supermomo31/PCE_colorlight_carrier/PCE_Colorlight_Carrier/av.kicad_sch

## KiCad design PCE_Colorlight_Carrier/av.kicad_sch (2026-05-21, an earlier design)

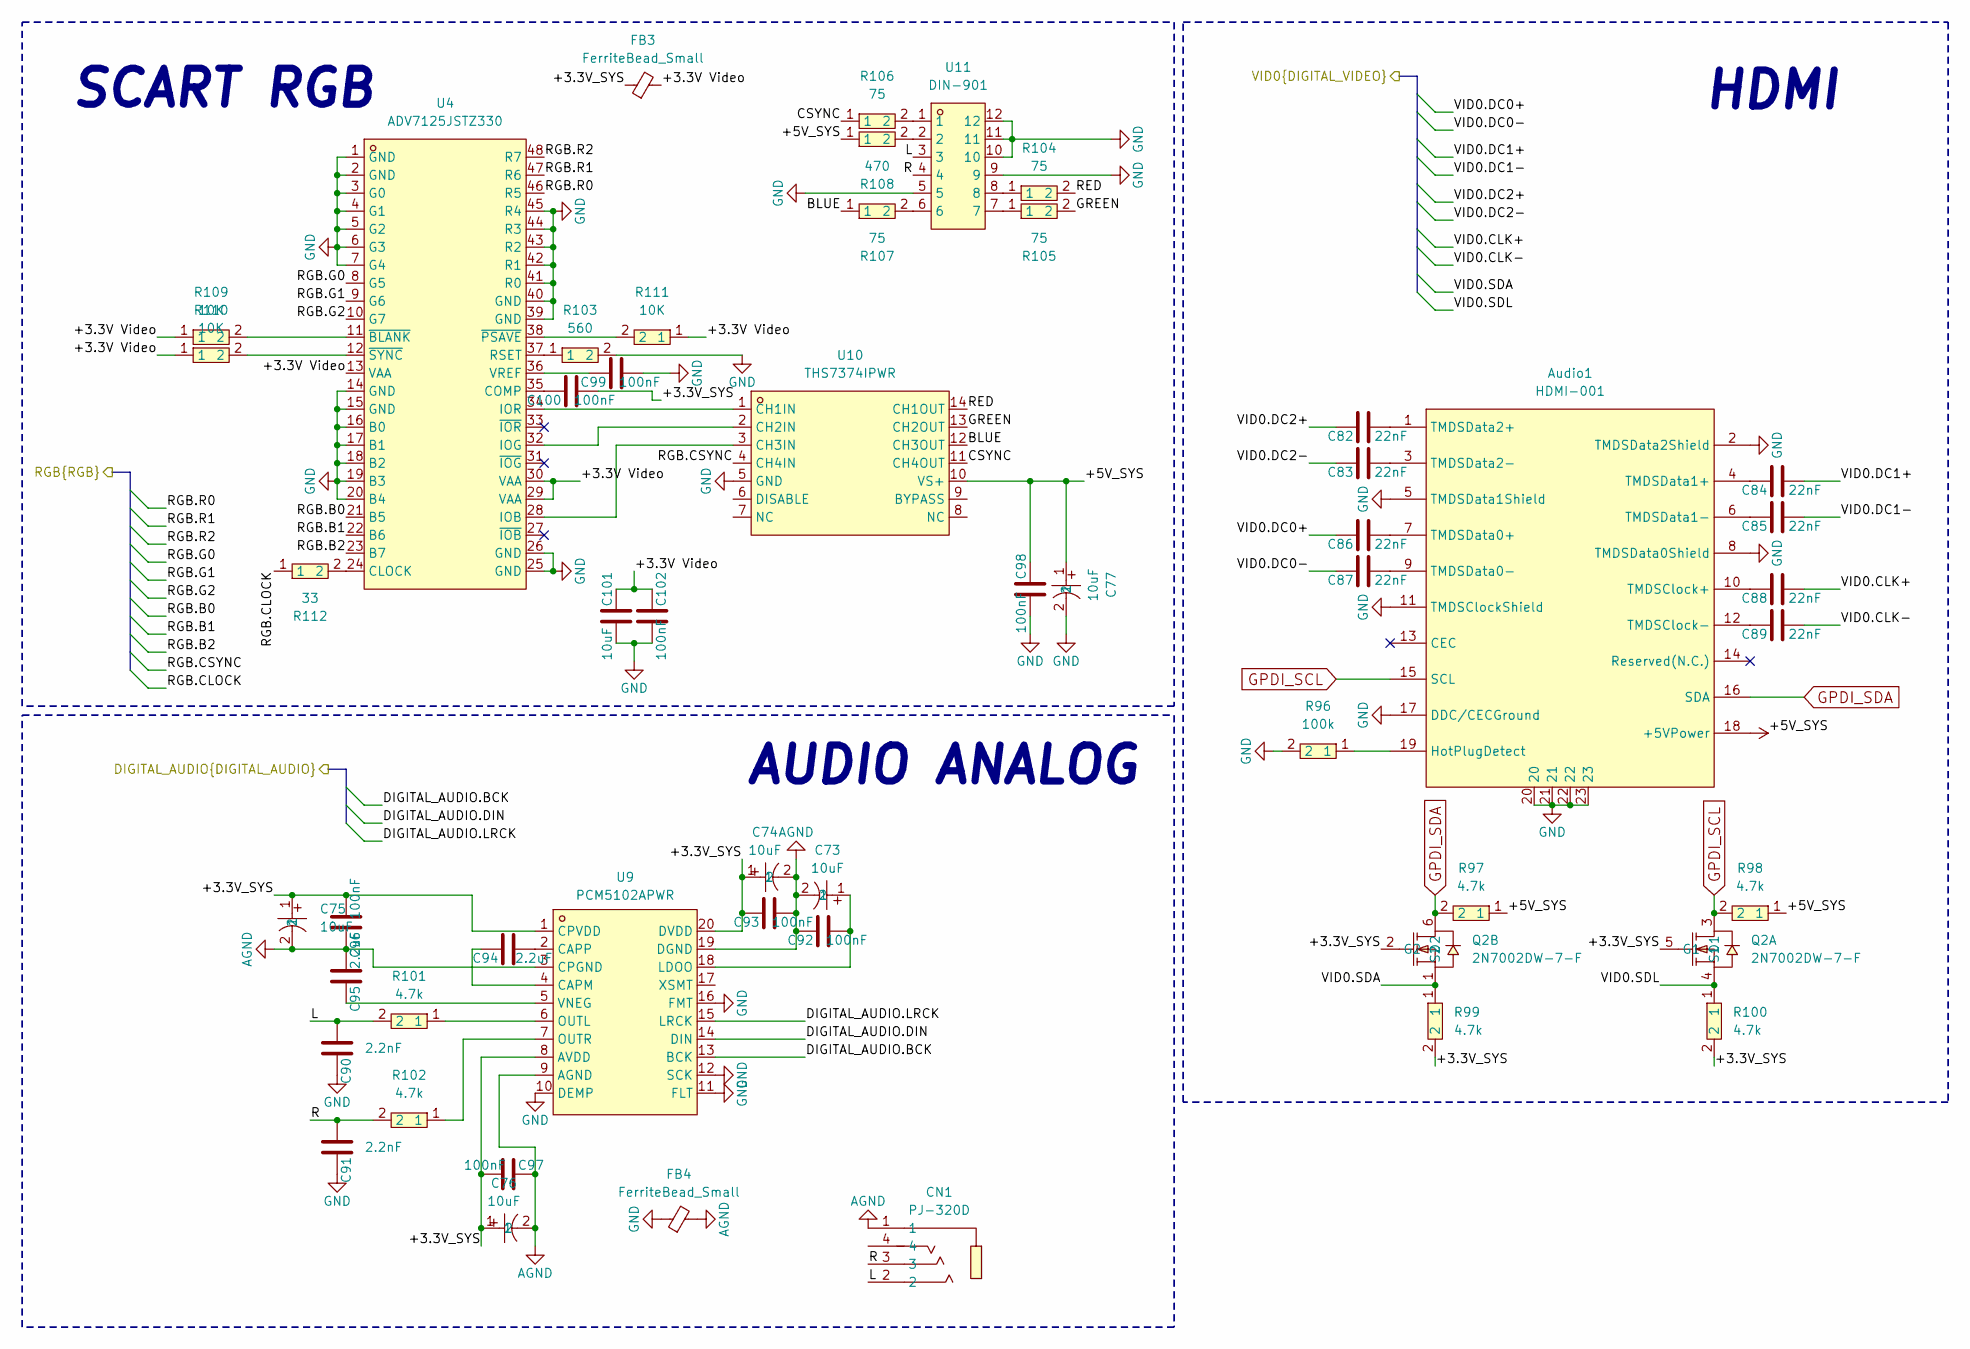
[picture p3: schematic av.kicad_sch]

Parts:
Audio1: HDMI-001; HDMI; MPN HDMI-001 19PCBTP; LCSC Part C138388
C73, C74, C75, C76, C77: 10uF; CAP-SMD_BD5.0-L5.3-W5.3-FD; MPN RVT1A101M0505; LCSC Part C3347
C82, C83, C84, C85, C86, C87, C88, C89: 22nF; C_0603_1608Metric
C90, C91: 2.2nF; C_0603_1608Metric
C92, C93, C96, C97, C98, C99, C100, C102: 100nF; C_0603_1608Metric
C94, C95: 2.2uF; C_0603_1608Metric
C101: 10uF; C_0603_1608Metric
CN1: PJ-320D; AUDIO-SMD_PJ-320D-1; MPN PJ-320D; LCSC Part C431535
FB3, FB4: FerriteBead_Small
Q2: 2N7002DW-7-F; SOT-363_L2.0-W1.3-P0.65-LS2.1-TL; MPN 2N7002DW-7-F; LCSC Part C83571
R96: 100k; R0603; MPN 0603WAF5101T5E; LCSC Part C23186
R97, R98, R99, R100, R101, R102: 4.7k; R0603; MPN 0603WAF5101T5E; LCSC Part C23186
R103: 560; R0603; MPN 0603WAF5101T5E; LCSC Part C23186
R104, R105, R106, R107: 75; R0603; MPN 0603WAF5101T5E; LCSC Part C23186
R108: 470; R0603; MPN 0603WAF5101T5E; LCSC Part C23186
R109, R110, R111: 10K; R0603; MPN 0603WAF5101T5E; LCSC Part C23186
R112: 33; R0603; MPN 0603WAF5101T5E; LCSC Part C23186
U4: ADV7125JSTZ330; LQFP-48_L7.0-W7.0-P0.50-LS9.0-BL; MPN ADV7125JSTZ330; LCSC Part C662165
U9: PCM5102APWR; MPN PCM5102APWR; LCSC Part C107671
U10: THS7374IPWR; MPN THS7374IPWR; LCSC Part C2652746
U11: DIN-901; mini din 9; MPN DIN-901; LCSC Part C23689425

Connections:
+3.3V Video: C101.1, C102.1, FB3.2, R109.1, R110.1, R111.1, U4.13 (VAA), U4.29 (VAA), U4.30 (VAA)
+3.3V_SYS: C74.1, C75.1, C76.1, C93.1, C96.2, C97.2, C100.2, FB3.1, Q2.2 (G2), Q2.5 (G1), R99.2, R100.2, U9.1 (CPVDD), U9.8 (AVDD), U9.20 (DVDD)
+5V: Audio1.18 (+5VPower)
+5V_SYS: C77.1, C98.1, R97.1, R98.1, R108.1, U10.10 (VS+)
AGND: C73.2, C74.2, C75.2, C76.2, C92.1, C93.2, C95.2, C96.1, C97.1, CN1.1, FB4.2, U9.3 (CPGND), U9.9 (AGND), U9.19 (DGND)
BLUE: R107.1, U10.12 (CH3OUT)
CSYNC: R106.1, U10.11 (CH4OUT)
DIGITAL_AUDIO.BCK: U9.13 (BCK)
DIGITAL_AUDIO.DIN: U9.14 (DIN)
DIGITAL_AUDIO.LRCK: U9.15 (LRCK)
GND: Audio1.2 (TMDSData2Shield), Audio1.5 (TMDSData1Shield), Audio1.8 (TMDSData0Shield), Audio1.11 (TMDSClockShield), Audio1.17 (DDC/CECGround), Audio1.20, Audio1.21, Audio1.22, Audio1.23, C77.2, C90.1, C91.1, C98.2, C99.2, C101.2, C102.2, FB4.1, R96.2, R103.2, U4.1 (GND), U4.2 (GND), U4.3 (G0), U4.4 (G1), U4.5 (G2), U4.6 (G3), U4.7 (G4), U4.14 (GND), U4.15 (GND), U4.16 (B0), U4.17 (B1), U4.18 (B2), U4.19 (B3), U4.20 (B4), U4.25 (GND), U4.26 (GND), U4.39 (GND), U4.40 (GND), U4.41 (R0), U4.42 (R1), U4.43 (R2), U4.44 (R3), U4.45 (R4), U9.10 (DEMP), U9.11 (FLT), U9.12 (SCK), U9.16 (FMT), U10.5 (GND), U11.5, U11.9, U11.10, U11.11, U11.12
GPDI_SCL: Audio1.15 (SCL), Q2.3 (D1), R98.2
GPDI_SDA: Audio1.16 (SDA), Q2.6 (D2), R97.2
GREEN: R105.2, U10.13 (CH2OUT)
L: C90.2, CN1.2, R101.2, U11.3
unnamed: Audio1.1 (TMDSData2+), C82.2
unnamed: Audio1.3 (TMDSData2-), C83.2
unnamed: Audio1.4 (TMDSData1+), C84.1
unnamed: Audio1.6 (TMDSData1-), C85.1
unnamed: Audio1.7 (TMDSData0+), C86.2
unnamed: Audio1.9 (TMDSData0-), C87.2
unnamed: Audio1.10 (TMDSClock+), C88.1
unnamed: Audio1.12 (TMDSClock-), C89.1
unnamed: Audio1.19 (HotPlugDetect), R96.1
unnamed: C73.1, C92.2, U9.18 (LDOO)
unnamed: C94.1, U9.4 (CAPM)
unnamed: C94.2, U9.2 (CAPP)
unnamed: C95.1, U9.5 (VNEG)
unnamed: C99.1, U4.36 (VREF)
unnamed: C100.1, U4.35 (COMP)
unnamed: R101.1, U9.6 (OUTL)
unnamed: R102.1, U9.7 (OUTR)
unnamed: R103.1, U4.37 (RSET)
unnamed: R104.1, U11.8
unnamed: R105.1, U11.7
unnamed: R106.2, U11.1
unnamed: R107.2, U11.6
unnamed: R108.2, U11.2
unnamed: R109.2, U4.11 (~BLANK)
unnamed: R110.2, U4.12 (~SYNC)
unnamed: R111.2, U4.38 (~PSAVE)
unnamed: R112.2, U4.24 (CLOCK)
unnamed: U4.34 (IOR), U10.1 (CH1IN)
unnamed: U4.32 (IOG), U10.2 (CH2IN)
unnamed: U4.28 (IOB), U10.3 (CH3IN)
R: C91.2, CN1.3, R102.2, U11.4
RED: R104.2, U10.14 (CH1OUT)
RGB.B0: U4.21 (B5)
RGB.B1: U4.22 (B6)
RGB.B2: U4.23 (B7)
RGB.CLOCK: R112.1
RGB.CSYNC: U10.4 (CH4IN)
RGB.G0: U4.8 (G5)
RGB.G1: U4.9 (G6)
RGB.G2: U4.10 (G7)
RGB.R0: U4.46 (R5)
RGB.R1: U4.47 (R6)
RGB.R2: U4.48 (R7)
VID0.CLK+: C88.2
VID0.CLK-: C89.2
VID0.DC0+: C86.1
VID0.DC0-: C87.1
VID0.DC1+: C84.2
VID0.DC1-: C85.2
VID0.DC2+: C82.1
VID0.DC2-: C83.1
VID0.SDA: Q2.1 (S2), R99.1
VID0.SDL: Q2.4 (S1), R100.1

Notes on the sheet:
AUDIO ANALOG
SCART RGB
HDMI
