supermomo31/PCE_colorlight_carrier/PCE_Colorlight_Carrier/core.kicad_sch

## KiCad design PCE_Colorlight_Carrier/core.kicad_sch (2026-05-21, an earlier design)

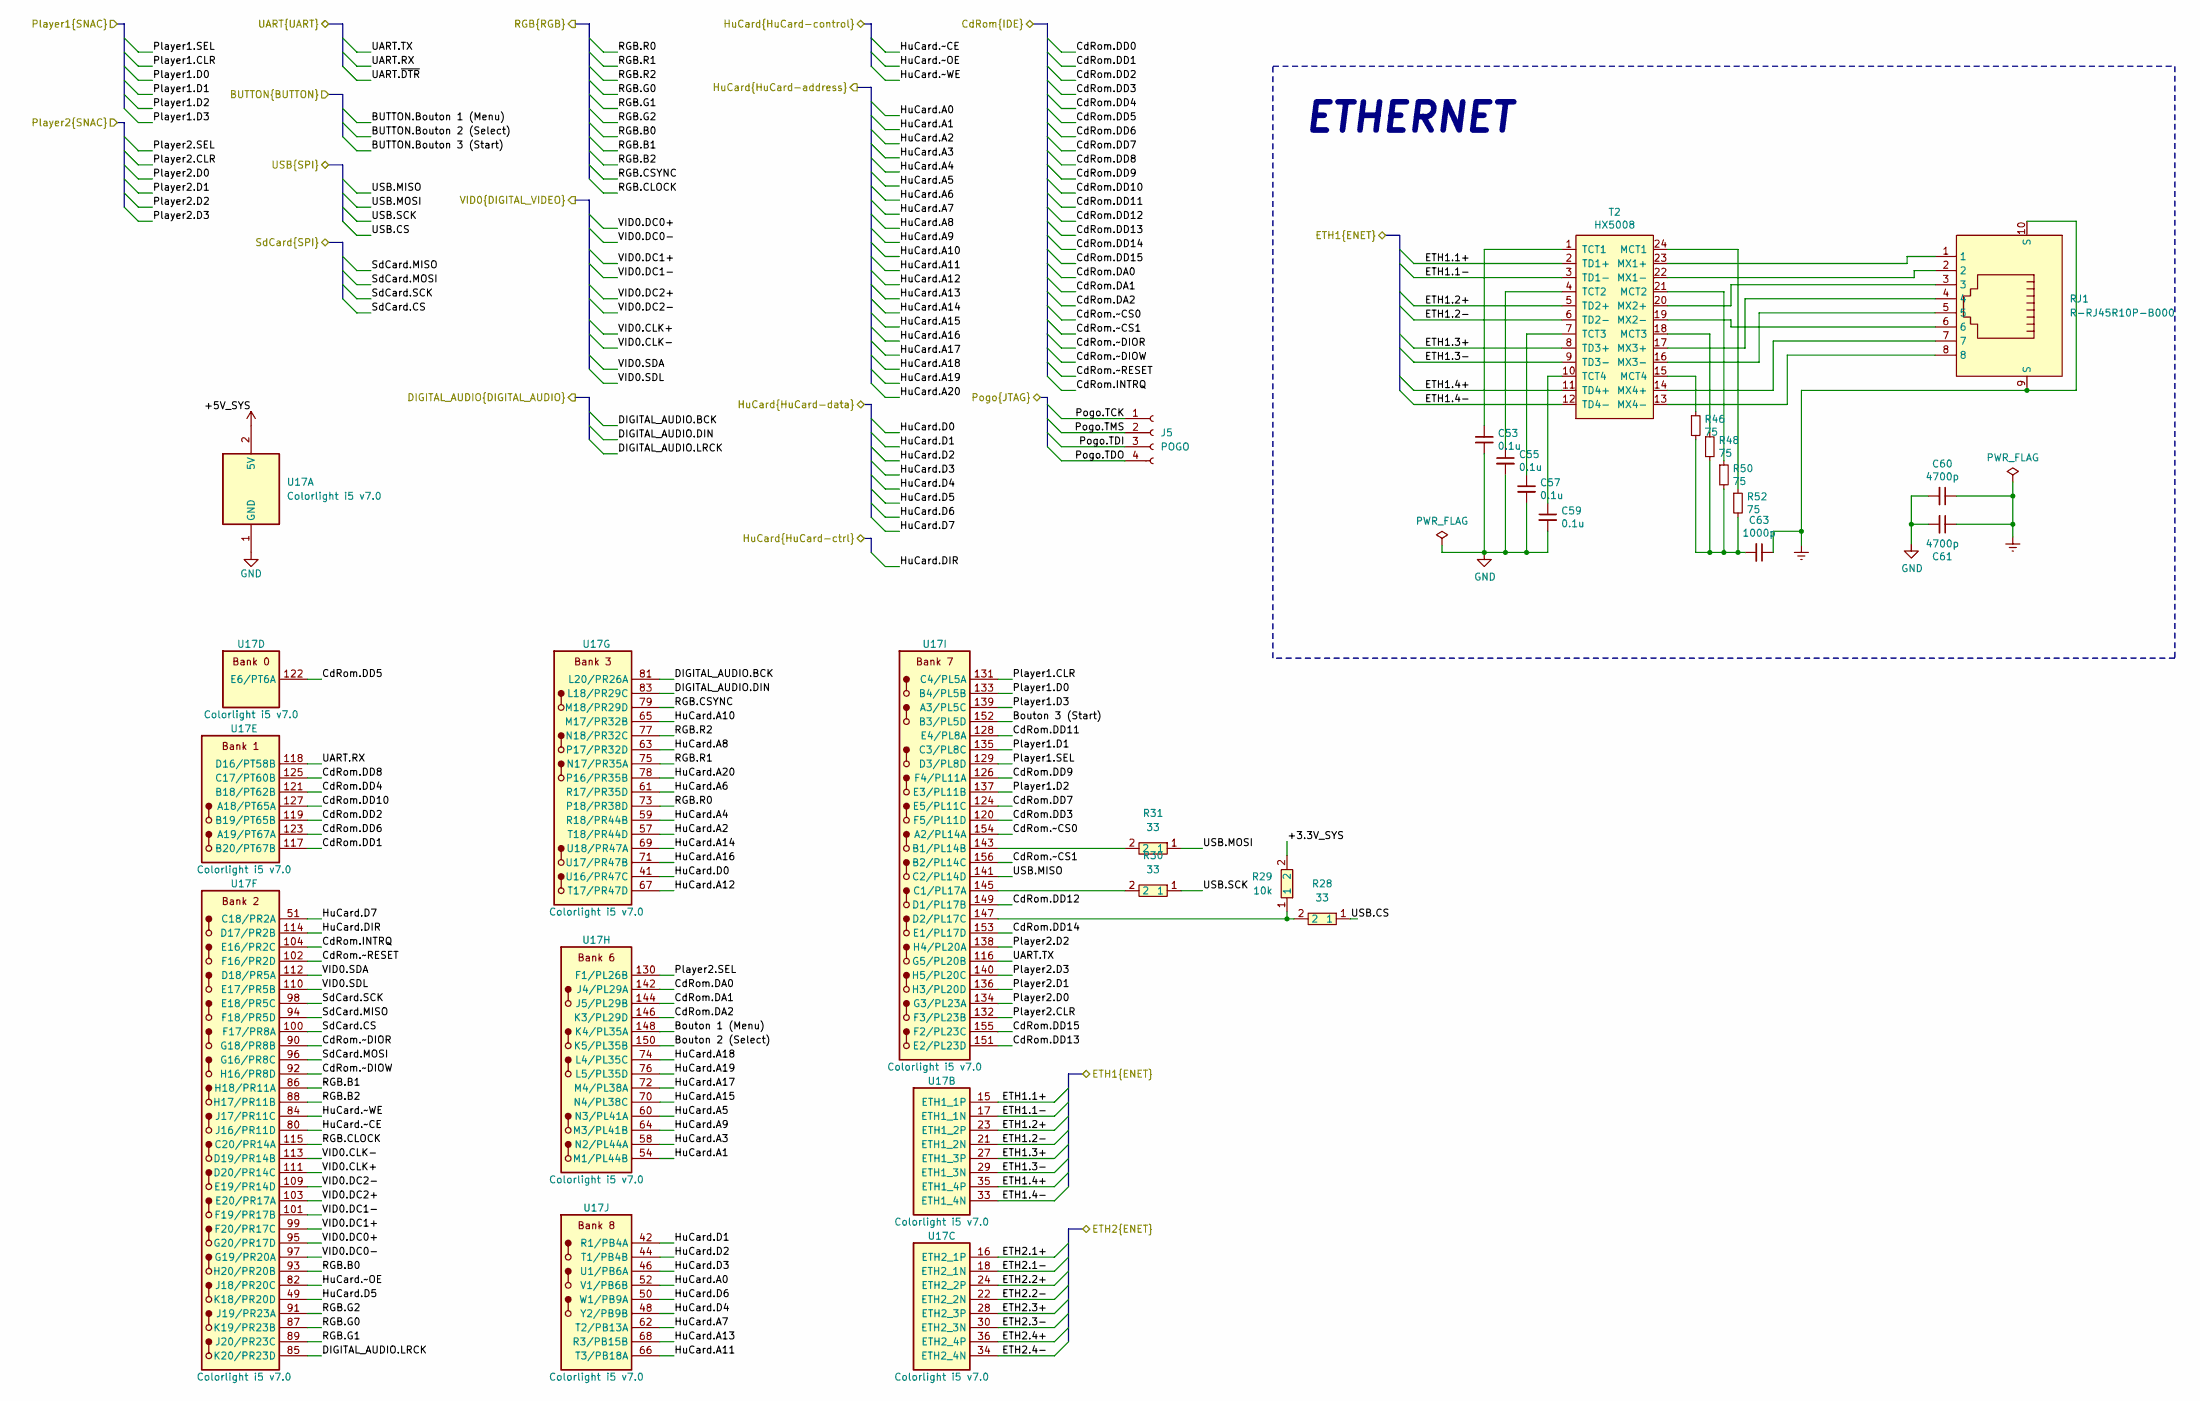
[picture p4: schematic core.kicad_sch]

Parts:
C53, C55, C57, C59: 0.1u; C_0402_1005Metric
C60, C61: 4700p; R_1812_4532Metric
C63: 1000p; C_0402_1005Metric
J5: POGO; PinHeader_1x04_P2.54mm_Vertical
R28, R30, R31: 33; R0603; MPN 0603WAF5101T5E; LCSC Part C23186
R29: 10k; R0603; MPN 0603WAF5101T5E; LCSC Part C23186
R46, R48, R50, R52: 75; R_0402_1005Metric
RJ1: R-RJ45R10P-B000; RJ45-TH_R-RJ45R10P-B000; MPN R-RJ45R10P-B000; LCSC Part C386758
T2: HX5008; HX5008NL
U17: Colorlight i5 v7.0; SO-DIMM-SMD_200P-P0.60_1473005-4

Connections:
+3.3V_SYS: R29.2
+5V: U17.2 (5V), U17.4 (5V), U17.6 (5V), U17.8 (5V), U17.10 (5V), U17.12 (5V)
Bouton 1 (Menu): U17.148 (K4/PL35A)
Bouton 2 (Select): U17.150 (K5/PL35B)
Bouton 3 (Start): U17.152 (B3/PL5D)
CdRom.DA0: U17.142 (J4/PL29A)
CdRom.DA1: U17.144 (J5/PL29B)
CdRom.DA2: U17.146 (K3/PL29D)
CdRom.DD1: U17.117 (B20/PT67B)
CdRom.DD2: U17.119 (B19/PT65B)
CdRom.DD3: U17.120 (F5/PL11D)
CdRom.DD4: U17.121 (B18/PT62B)
CdRom.DD5: U17.122 (E6/PT6A)
CdRom.DD6: U17.123 (A19/PT67A)
CdRom.DD7: U17.124 (E5/PL11C)
CdRom.DD8: U17.125 (C17/PT60B)
CdRom.DD9: U17.126 (F4/PL11A)
CdRom.DD10: U17.127 (A18/PT65A)
CdRom.DD11: U17.128 (E4/PL8A)
CdRom.DD12: U17.149 (D1/PL17B)
CdRom.DD13: U17.151 (E2/PL23D)
CdRom.DD14: U17.153 (E1/PL17D)
CdRom.DD15: U17.155 (F2/PL23C)
CdRom.INTRQ: U17.104 (E16/PR2C)
CdRom.~CS0: U17.154 (A2/PL14A)
CdRom.~CS1: U17.156 (B2/PL14C)
CdRom.~DIOR: U17.90 (G18/PR8B)
CdRom.~DIOW: U17.92 (H16/PR8D)
CdRom.~RESET: U17.102 (F16/PR2D)
DIGITAL_AUDIO.BCK: U17.81 (L20/PR26A)
DIGITAL_AUDIO.DIN: U17.83 (L18/PR29C)
DIGITAL_AUDIO.LRCK: U17.85 (K20/PR23D)
ETH1.1+: T2.2 (TD1+), U17.15 (ETH1_1P)
ETH1.1-: T2.3 (TD1-), U17.17 (ETH1_1N)
ETH1.2+: T2.5 (TD2+), U17.23 (ETH1_2P)
ETH1.2-: T2.6 (TD2-), U17.21 (ETH1_2N)
ETH1.3+: T2.8 (TD3+), U17.27 (ETH1_3P)
ETH1.3-: T2.9 (TD3-), U17.29 (ETH1_3N)
ETH1.4+: T2.11 (TD4+), U17.35 (ETH1_4P)
ETH1.4-: T2.12 (TD4-), U17.33 (ETH1_4N)
ETH2.1+: U17.16 (ETH2_1P)
ETH2.1-: U17.18 (ETH2_1N)
ETH2.2+: U17.24 (ETH2_2P)
ETH2.2-: U17.22 (ETH2_2N)
ETH2.3+: U17.28 (ETH2_3P)
ETH2.3-: U17.30 (ETH2_3N)
ETH2.4+: U17.36 (ETH2_4P)
ETH2.4-: U17.34 (ETH2_4N)
Earth: C60.1, C61.1, C63.1, RJ1.9 (S), RJ1.10 (S)
GND: C53.2, C55.2, C57.2, C59.2, C60.2, C61.2, U17.1 (GND), U17.3 (GND), U17.5 (GND), U17.7 (GND), U17.9 (GND), U17.11 (GND), U17.39 (GND), U17.40 (GND), U17.55 (GND), U17.56 (GND), U17.105 (GND), U17.106 (GND), U17.107 (GND), U17.108 (GND), U17.157 (GND), U17.158 (GND), U17.199 (GND), U17.200 (GND)
HuCard.A0: U17.52 (V1/PB6B)
HuCard.A1: U17.54 (M1/PL44B)
HuCard.A2: U17.57 (T18/PR44D)
HuCard.A3: U17.58 (N2/PL44A)
HuCard.A4: U17.59 (R18/PR44B)
HuCard.A5: U17.60 (N3/PL41A)
HuCard.A6: U17.61 (R17/PR35D)
HuCard.A7: U17.62 (T2/PB13A)
HuCard.A8: U17.63 (P17/PR32D)
HuCard.A9: U17.64 (M3/PL41B)
HuCard.A10: U17.65 (M17/PR32B)
HuCard.A11: U17.66 (T3/PB18A)
HuCard.A12: U17.67 (T17/PR47D)
HuCard.A13: U17.68 (R3/PB15B)
HuCard.A14: U17.69 (U18/PR47A)
HuCard.A15: U17.70 (N4/PL38C)
HuCard.A16: U17.71 (U17/PR47B)
HuCard.A17: U17.72 (M4/PL38A)
HuCard.A18: U17.74 (L4/PL35C)
HuCard.A19: U17.76 (L5/PL35D)
HuCard.A20: U17.78 (P16/PR35B)
HuCard.D0: U17.41 (U16/PR47C)
HuCard.D1: U17.42 (R1/PB4A)
HuCard.D2: U17.44 (T1/PB4B)
HuCard.D3: U17.46 (U1/PB6A)
HuCard.D4: U17.48 (Y2/PB9B)
HuCard.D5: U17.49 (K18/PR20D)
HuCard.D6: U17.50 (W1/PB9A)
HuCard.D7: U17.51 (C18/PR2A)
HuCard.DIR: U17.114 (D17/PR2B)
HuCard.~CE: U17.80 (J16/PR11D)
HuCard.~OE: U17.82 (J18/PR20C)
HuCard.~WE: U17.84 (J17/PR11C)
unnamed: C53.1, T2.1 (TCT1)
unnamed: C55.1, T2.4 (TCT2)
unnamed: C57.1, T2.7 (TCT3)
unnamed: C59.1, T2.10 (TCT4)
unnamed: C63.2, R46.2, R48.2, R50.2, R52.2
unnamed: R28.2, R29.1, U17.147 (D2/PL17C)
unnamed: R30.2, U17.145 (C1/PL17A)
unnamed: R31.2, U17.143 (B1/PL14B)
unnamed: R46.1, T2.15 (MCT4)
unnamed: R48.1, T2.18 (MCT3)
unnamed: R50.1, T2.21 (MCT2)
unnamed: R52.1, T2.24 (MCT1)
unnamed: RJ1.1, T2.23 (MX1+)
unnamed: RJ1.2, T2.22 (MX1-)
unnamed: RJ1.3, T2.20 (MX2+)
unnamed: RJ1.4, T2.17 (MX3+)
unnamed: RJ1.5, T2.16 (MX3-)
unnamed: RJ1.6, T2.19 (MX2-)
unnamed: RJ1.7, T2.14 (MX4+)
unnamed: RJ1.8, T2.13 (MX4-)
Player1.CLR: U17.131 (C4/PL5A)
Player1.D0: U17.133 (B4/PL5B)
Player1.D1: U17.135 (C3/PL8C)
Player1.D2: U17.137 (E3/PL11B)
Player1.D3: U17.139 (A3/PL5C)
Player1.SEL: U17.129 (D3/PL8D)
Player2.CLR: U17.132 (F3/PL23B)
Player2.D0: U17.134 (G3/PL23A)
Player2.D1: U17.136 (H3/PL20D)
Player2.D2: U17.138 (H4/PL20A)
Player2.D3: U17.140 (H5/PL20C)
Player2.SEL: U17.130 (F1/PL26B)
Pogo.TCK: J5.1
Pogo.TDI: J5.3
Pogo.TDO: J5.4
Pogo.TMS: J5.2
RGB.B0: U17.93 (H20/PR20B)
RGB.B1: U17.86 (H18/PR11A)
RGB.B2: U17.88 (H17/PR11B)
RGB.CLOCK: U17.115 (C20/PR14A)
RGB.CSYNC: U17.79 (M18/PR29D)
RGB.G0: U17.87 (K19/PR23B)
RGB.G1: U17.89 (J20/PR23C)
RGB.G2: U17.91 (J19/PR23A)
RGB.R0: U17.73 (P18/PR38D)
RGB.R1: U17.75 (N17/PR35A)
RGB.R2: U17.77 (N18/PR32C)
SdCard.CS: U17.100 (F17/PR8A)
SdCard.MISO: U17.94 (F18/PR5D)
SdCard.MOSI: U17.96 (G16/PR8C)
SdCard.SCK: U17.98 (E18/PR5C)
UART.RX: U17.118 (D16/PT58B)
UART.TX: U17.116 (G5/PL20B)
USB.CS: R28.1
USB.MISO: U17.141 (C2/PL14D)
USB.MOSI: R31.1
USB.SCK: R30.1
VID0.CLK+: U17.111 (D20/PR14C)
VID0.CLK-: U17.113 (D19/PR14B)
VID0.DC0+: U17.95 (G20/PR17D)
VID0.DC0-: U17.97 (G19/PR20A)
VID0.DC1+: U17.99 (F20/PR17C)
VID0.DC1-: U17.101 (F19/PR17B)
VID0.DC2+: U17.103 (E20/PR17A)
VID0.DC2-: U17.109 (E19/PR14D)
VID0.SDA: U17.112 (D18/PR5A)
VID0.SDL: U17.110 (E17/PR5B)

Notes on the sheet:
ETHERNET
