supermomo31/PCE_colorlight_carrier/PCE_Colorlight_Carrier/front_io.kicad_sch

## KiCad design PCE_Colorlight_Carrier/front_io.kicad_sch (2026-05-21, an earlier design)

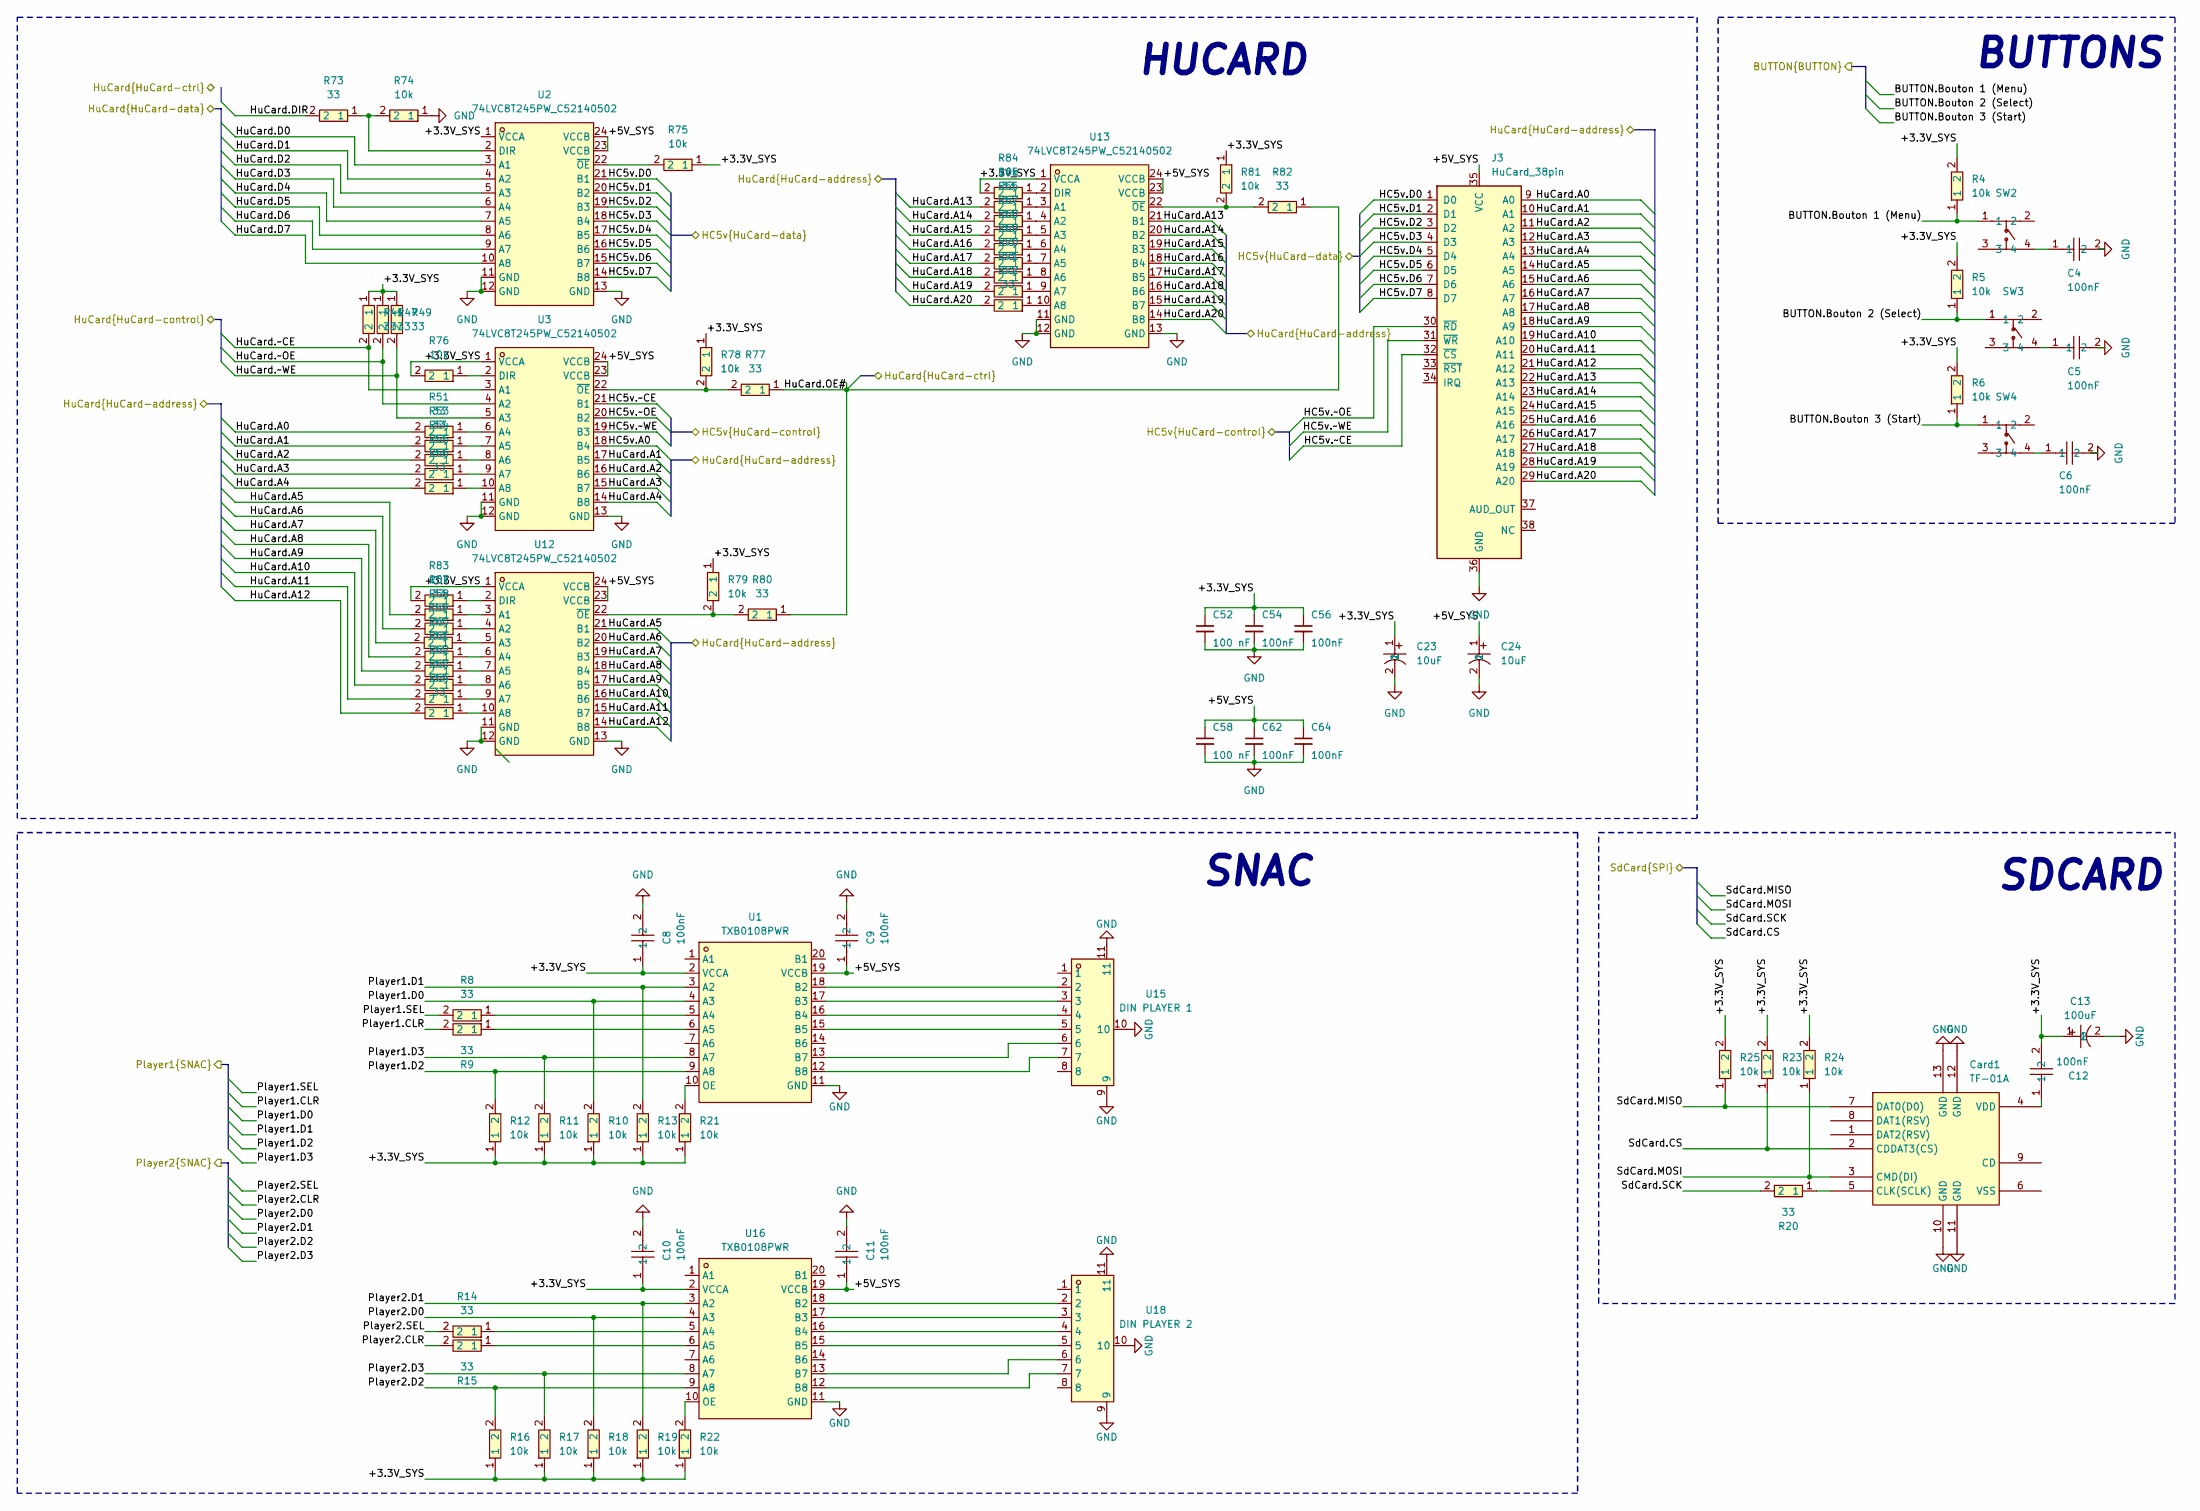
[picture p5: schematic front_io.kicad_sch]

Parts:
C4, C5, C6, C8, C9, C10, C11, C12: 100nF; R0603; MPN CL10A106KP8NNNC; LCSC Part C19702
C13: 100uF; CAP-SMD_BD5.0-L5.3-W5.3-FD; MPN RVT1A101M0505; LCSC Part C3347
C23, C24: 10uF; CAP-SMD_BD5.0-L5.3-W5.3-FD; MPN RVT1A101M0505; LCSC Part C3347
C52, C58: 100 nF; C_0402_1005Metric; LCSC C52923
C54, C56, C62, C64: 100nF; C_0402_1005Metric; LCSC C1525
Card1: TF-01A; SD; MPN TF-01A; LCSC Part C91145
J3: HuCard_38pin; HUC_Connector_JTStudio
R4, R5, R6, R10, R11, R12, R13, R16, R17, R18, R19, R21, R22, R23, R24, R25, R74, R75, R76, R78, R79, R81, R83, R84: 10k; R0603; MPN 0603WAF5101T5E; LCSC Part C23186
R8, R9, R14, R15, R20, R41, R47, R49, R51, R53, R54, R55, R56, R57, R58, R59, R60, R61, R62, R63, R64, R65, R66, R67, R68, R69, R70, R71, R72, R73, R77, R80, R82: 33; R0603; MPN 0603WAF5101T5E; LCSC Part C23186
SW2, SW3, SW4: HX 5.2X5.2X2.0H SWITCH TACTILE SPST-NO 0.05A 12V; SW-SMD; MPN HX 5.2x5.2x2.0H SWITCH TACTILE SPST-NO 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; LCSC Part C49234134
U1, U16: TXB0108PWR; MPN TXB0108PWR; LCSC Part C53406
U2, U3, U12, U13: 74LVC8T245PW_C52140502; 74LVC245APW; MPN 74LVC8T245PW; LCSC Part C52140502
U15: DIN PLAYER 1; CONN-TH_DIN-802; MPN DIN-802; LCSC Part C41409494
U18: DIN PLAYER 2; CONN-TH_DIN-802; MPN DIN-802; LCSC Part C41409494

Connections:
+3.3V_SYS: C8.1, C10.1, C12.2, C13.1, C23.1, C52.1, C54.1, C56.1, R4.2, R5.2, R6.2, R10.1, R11.1, R12.1, R13.1, R16.1, R17.1, R18.1, R19.1, R21.1, R22.1, R23.2, R24.2, R25.2, R41.1, R47.1, R49.1, R75.1, R76.2, R78.1, R79.1, R81.1, R83.2, R84.2, U1.2 (VCCA), U2.1 (VCCA), U3.1 (VCCA), U12.1 (VCCA), U13.1 (VCCA), U16.2 (VCCA)
+5V_SYS: C9.1, C11.1, C24.1, C58.1, C62.1, C64.1, J3.35 (VCC), U1.19 (VCCB), U2.23 (VCCB), U2.24 (VCCB), U3.23 (VCCB), U3.24 (VCCB), U12.23 (VCCB), U12.24 (VCCB), U13.23 (VCCB), U13.24 (VCCB), U16.19 (VCCB)
BUTTON.Bouton 1 (Menu): R4.1, SW2.1
BUTTON.Bouton 2 (Select): R5.1, SW3.1
BUTTON.Bouton 3 (Start): R6.1, SW4.1
GND: C4.2, C5.2, C6.2, C8.2, C9.2, C10.2, C11.2, C13.2, C23.2, C24.2, C52.2, C54.2, C56.2, C58.2, C62.2, C64.2, Card1.10 (GND), Card1.11 (GND), Card1.12 (GND), Card1.13 (GND), J3.36 (GND), R74.1, U1.11 (GND), U2.11 (GND), U2.12 (GND), U2.13 (GND), U3.11 (GND), U3.12 (GND), U3.13 (GND), U12.11 (GND), U12.12 (GND), U12.13 (GND), U13.11 (GND), U13.12 (GND), U13.13 (GND), U15.9, U15.10, U15.11, U16.11 (GND), U18.9, U18.10, U18.11
HC5v.A0: U3.18 (B4)
HC5v.D0: J3.1 (D0), U2.21 (B1)
HC5v.D1: J3.2 (D1), U2.20 (B2)
HC5v.D2: J3.3 (D2), U2.19 (B3)
HC5v.D3: J3.4 (D3), U2.18 (B4)
HC5v.D4: J3.5 (D4), U2.17 (B5)
HC5v.D5: J3.6 (D5), U2.16 (B6)
HC5v.D6: J3.7 (D6), U2.15 (B7)
HC5v.D7: J3.8 (D7), U2.14 (B8)
HC5v.~CE: J3.32 (~CS), U3.21 (B1)
HC5v.~OE: J3.30 (~RD), U3.20 (B2)
HC5v.~WE: J3.31 (~WR), U3.19 (B3)
HuCard.A0: J3.9 (A0), R51.2
HuCard.A1: J3.10 (A1), R53.2, U3.17 (B5)
HuCard.A2: J3.11 (A2), R54.2, U3.16 (B6)
HuCard.A3: J3.12 (A3), R55.2, U3.15 (B7)
HuCard.A4: J3.13 (A4), R56.2, U3.14 (B8)
HuCard.A5: J3.14 (A5), R57.2, U12.21 (B1)
HuCard.A6: J3.15 (A6), R58.2, U12.20 (B2)
HuCard.A7: J3.16 (A7), R59.2, U12.19 (B3)
HuCard.A8: J3.17 (A8), R60.2, U12.18 (B4)
HuCard.A9: J3.18 (A9), R61.2, U12.17 (B5)
HuCard.A10: J3.19 (A10), R62.2, U12.16 (B6)
HuCard.A11: J3.20 (A11), R63.2, U12.15 (B7)
HuCard.A12: J3.21 (A12), R64.2, U12.14 (B8)
HuCard.A13: J3.22 (A13), R65.2, U13.21 (B1)
HuCard.A14: J3.23 (A14), R66.2, U13.20 (B2)
HuCard.A15: J3.24 (A15), R67.2, U13.19 (B3)
HuCard.A16: J3.25 (A16), R68.2, U13.18 (B4)
HuCard.A17: J3.26 (A17), R69.2, U13.17 (B5)
HuCard.A18: J3.27 (A18), R70.2, U13.16 (B6)
HuCard.A19: J3.28 (A19), R71.2, U13.15 (B7)
HuCard.A20: J3.29 (A20), R72.2, U13.14 (B8)
HuCard.D0: U2.3 (A1)
HuCard.D1: U2.4 (A2)
HuCard.D2: U2.5 (A3)
HuCard.D3: U2.6 (A4)
HuCard.D4: U2.7 (A5)
HuCard.D5: U2.8 (A6)
HuCard.D6: U2.9 (A7)
HuCard.D7: U2.10 (A8)
HuCard.DIR: R73.2
HuCard.OE#: R77.1, R80.1, R82.1
HuCard.~CE: R41.2, U3.3 (A1)
HuCard.~OE: R47.2, U3.4 (A2)
HuCard.~WE: R49.2, U3.5 (A3)
unnamed: C4.1, SW2.4
unnamed: C5.1, SW3.4
unnamed: C6.1, SW4.4
unnamed: C12.1, Card1.4 (VDD)
unnamed: Card1.5 (CLK(SCLK)), R20.1
unnamed: R8.1, U1.5 (A4)
unnamed: R9.1, U1.6 (A5)
unnamed: R14.1, U16.5 (A4)
unnamed: R15.1, U16.6 (A5)
unnamed: R21.2, U1.10 (OE)
unnamed: R22.2, U16.10 (OE)
unnamed: R51.1, U3.6 (A4)
unnamed: R53.1, U3.7 (A5)
unnamed: R54.1, U3.8 (A6)
unnamed: R55.1, U3.9 (A7)
unnamed: R56.1, U3.10 (A8)
unnamed: R57.1, U12.3 (A1)
unnamed: R58.1, U12.4 (A2)
unnamed: R59.1, U12.5 (A3)
unnamed: R60.1, U12.6 (A4)
unnamed: R61.1, U12.7 (A5)
unnamed: R62.1, U12.8 (A6)
unnamed: R63.1, U12.9 (A7)
unnamed: R64.1, U12.10 (A8)
unnamed: R65.1, U13.3 (A1)
unnamed: R66.1, U13.4 (A2)
unnamed: R67.1, U13.5 (A3)
unnamed: R68.1, U13.6 (A4)
unnamed: R69.1, U13.7 (A5)
unnamed: R70.1, U13.8 (A6)
unnamed: R71.1, U13.9 (A7)
unnamed: R72.1, U13.10 (A8)
unnamed: R73.1, R74.2, U2.2 (DIR)
unnamed: R75.2, U2.22 (~OE)
unnamed: R76.1, U3.2 (DIR)
unnamed: R77.2, R78.2, U3.22 (~OE)
unnamed: R79.2, R80.2, U12.22 (~OE)
unnamed: R81.2, R82.2, U13.22 (~OE)
unnamed: R83.1, U12.2 (DIR)
unnamed: R84.1, U13.2 (DIR)
unnamed: U1.12 (B8), U15.7
unnamed: U1.13 (B7), U15.6
unnamed: U1.15 (B5), U15.5
unnamed: U1.16 (B4), U15.4
unnamed: U1.17 (B3), U15.3
unnamed: U1.18 (B2), U15.2
unnamed: U16.12 (B8), U18.7
unnamed: U16.13 (B7), U18.6
unnamed: U16.15 (B5), U18.5
unnamed: U16.16 (B4), U18.4
unnamed: U16.17 (B3), U18.3
unnamed: U16.18 (B2), U18.2
Player1.CLR: R9.2
Player1.D0: R10.2, U1.4 (A3)
Player1.D1: R13.2, U1.3 (A2)
Player1.D2: R12.2, U1.9 (A8)
Player1.D3: R11.2, U1.8 (A7)
Player1.SEL: R8.2
Player2.CLR: R15.2
Player2.D0: R18.2, U16.4 (A3)
Player2.D1: R19.2, U16.3 (A2)
Player2.D2: R16.2, U16.9 (A8)
Player2.D3: R17.2, U16.8 (A7)
Player2.SEL: R14.2
SdCard.CS: Card1.2 (CDDAT3(CS)), R23.1
SdCard.MISO: Card1.7 (DAT0(D0)), R25.1
SdCard.MOSI: Card1.3 (CMD(DI)), R24.1
SdCard.SCK: R20.2

Notes on the sheet:
BUTTONS
SNAC
HUCARD
SDCARD
