supermomo31/PCE_colorlight_carrier/PCE_Colorlight_Carrier/power.kicad_sch

## KiCad design PCE_Colorlight_Carrier/power.kicad_sch (2026-05-21, an earlier design)

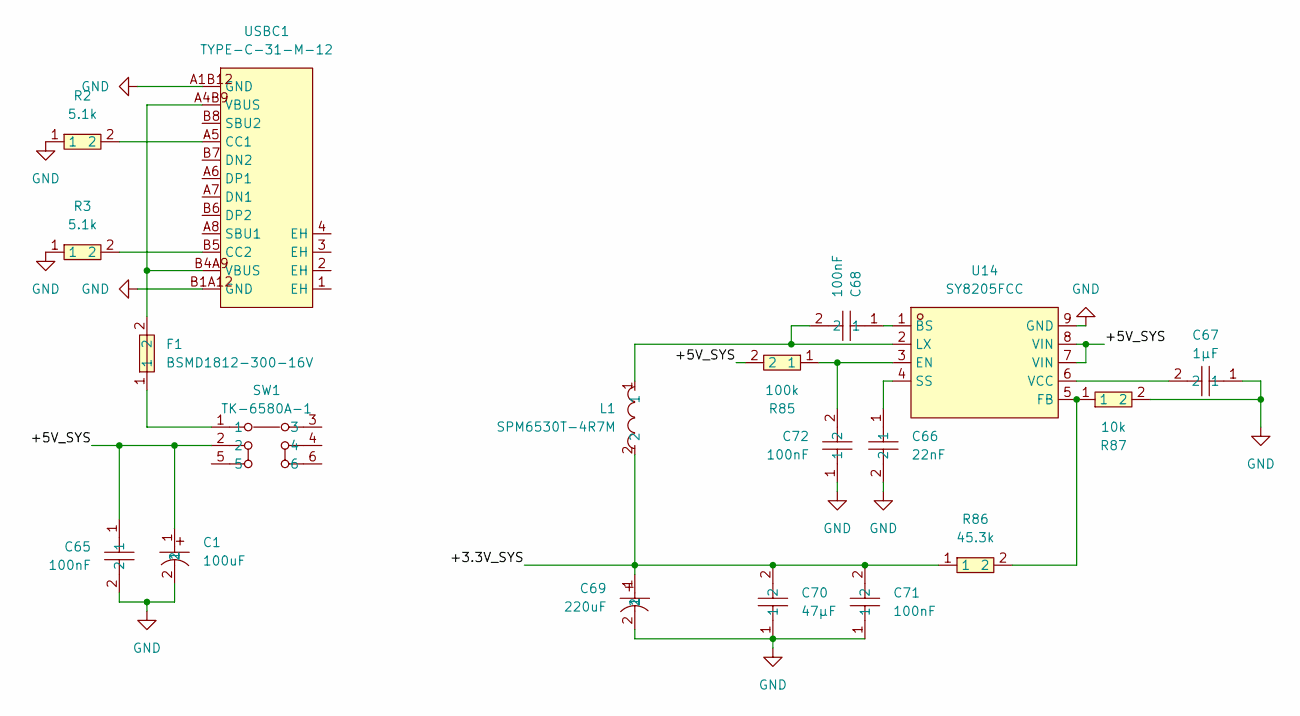
[picture p6: schematic power.kicad_sch]

Parts:
C1: 100uF; CAP-SMD_BD5.0-L5.3-W5.3-FD; MPN RVT1A101M0505; LCSC Part C3347
C65, C68, C71, C72: 100nF; R0603; MPN CL10A106KP8NNNC; LCSC Part C19702
C66: 22nF; R0603; MPN CL10A106KP8NNNC; LCSC Part C19702
C67: 1µF; R0603; MPN CL10A106KP8NNNC; LCSC Part C19702
C69: 220uF; CAP-SMD_BD5.0-L5.3-W5.3-FD; MPN RVT1A101M0505; LCSC Part C3347
C70: 47µF; R0603; MPN CL10A106KP8NNNC; LCSC Part C19702
F1: BSMD1812-300-16V; fuse; MPN BSMD1812-300-16V; LCSC Part C883162
L1: SPM6530T-4R7M; IND-SMD_L7.1-W6.5; MPN SPM6530T-4R7M; LCSC Part C76857
R2, R3: 5.1k; R0603; MPN 0603WAF5101T5E; LCSC Part C23186
R85: 100k; R0603; MPN 0603WAF5101T5E; LCSC Part C23186
R86: 45.3k; R0603; MPN 0603WAF5101T5E; LCSC Part C23186
R87: 10k; R0603; MPN 0603WAF5101T5E; LCSC Part C23186
SW1: TK-6580A-1; SWITCH; MPN TK-6580A-1; LCSC Part C528770
U14: SY8205FCC; SOIC-8_L5.0-W4.0-P1.27-LS6.0-BL-EP2.0; MPN SY8205FCC; LCSC Part C111875
USBC1: TYPE-C-31-M-12; USB-C_SMD-TYPE-C-31-M-12_1; MPN TYPE-C-31-M-12; LCSC Part C165948

Connections:
+3.3V_SYS: C69.1, C70.2, C71.2, L1.2, R86.1
+5V_SYS: C1.1, C65.1, R85.2, SW1.2, U14.7 (VIN), U14.8 (VIN)
GND: C1.2, C65.2, C66.2, C67.1, C69.2, C70.1, C71.1, C72.1, R2.1, R3.1, R87.2, U14.9 (GND), USBC1.A1B12 (GND), USBC1.B1A12 (GND)
unnamed: C66.1, U14.4 (SS)
unnamed: C67.2, U14.6 (VCC)
unnamed: C68.1, U14.1 (BS)
unnamed: C68.2, L1.1, U14.2 (LX)
unnamed: C72.2, R85.1, U14.3 (EN)
unnamed: F1.1, SW1.1
unnamed: F1.2, USBC1.A4B9 (VBUS), USBC1.B4A9 (VBUS)
unnamed: R2.2, USBC1.A5 (CC1)
unnamed: R3.2, USBC1.B5 (CC2)
unnamed: R86.2, R87.1, U14.5 (FB)
