supermomo31/PCE_colorlight_carrier/PCE_Colorlight_Carrier/usb_JTAG-UART.kicad_sch

## KiCad design PCE_Colorlight_Carrier/usb_JTAG-UART.kicad_sch (2026-05-21, an earlier design)

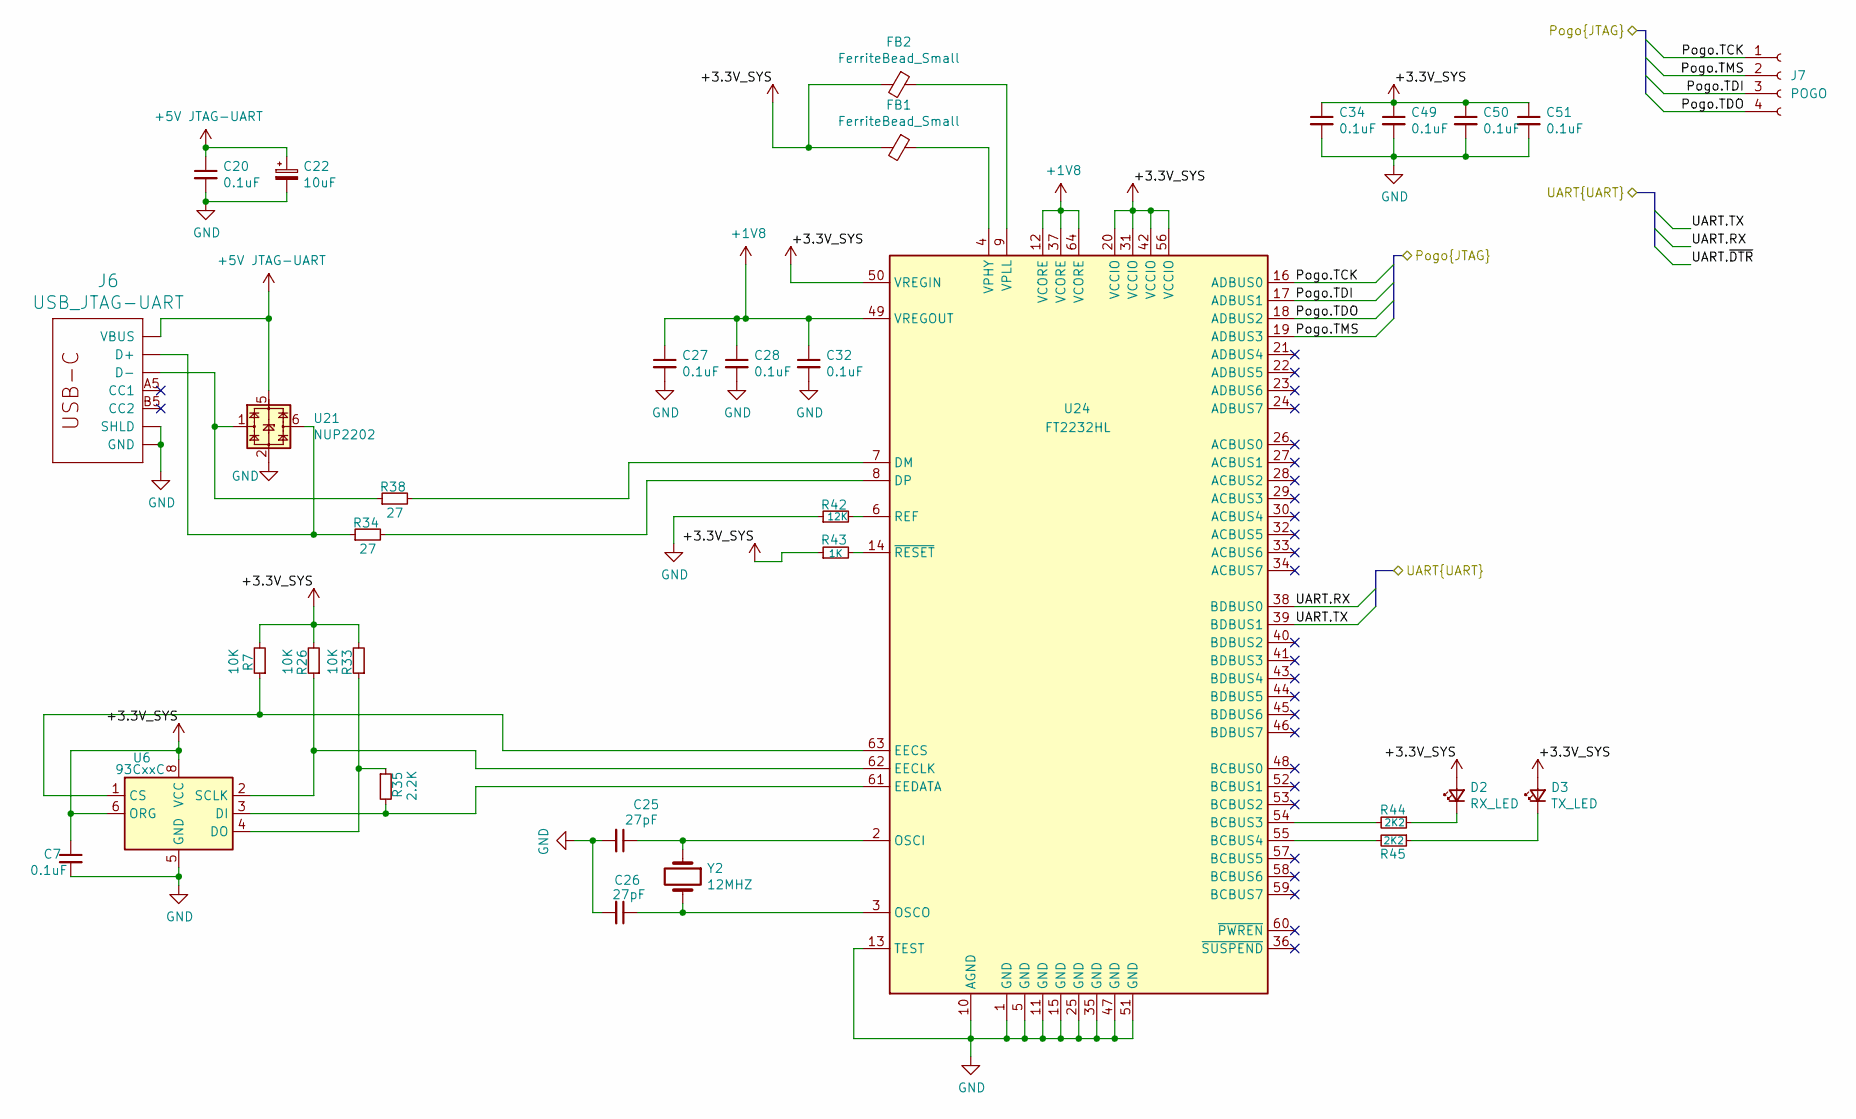
[picture p7: schematic usb_JTAG-UART.kicad_sch]

Parts:
C7, C20, C27, C28, C32, C34, C49, C50, C51: 0.1uF; C_0805_2012Metric_Pad1.18x1.45mm_HandSolder
C22: 10uF; CP_EIA-3216-18_Kemet-A_Pad1.58x1.35mm_HandSolder
C25, C26: 27pF; C_0805_2012Metric_Pad1.18x1.45mm_HandSolder
D2: RX_LED; LED_0805_2012Metric_Pad1.15x1.40mm_HandSolder
D3: TX_LED; LED_0805_2012Metric_Pad1.15x1.40mm_HandSolder
FB1, FB2: FerriteBead_Small; L_0805_2012Metric_Pad1.15x1.40mm_HandSolder
J6: USB_JTAG-UART; USB-C-COM-15111
J7: POGO; PinHeader_1x04_P2.54mm_Vertical
R7, R26, R33: 10K; R_0805_2012Metric_Pad1.20x1.40mm_HandSolder
R34, R38: 27; R_0805_2012Metric_Pad1.20x1.40mm_HandSolder
R35: 2.2K; R_0805_2012Metric_Pad1.20x1.40mm_HandSolder
R42: 12K; R_0805_2012Metric_Pad1.20x1.40mm_HandSolder
R43: 1K; R_0805_2012Metric_Pad1.20x1.40mm_HandSolder
R44, R45: 2K2; R_0805_2012Metric_Pad1.20x1.40mm_HandSolder
U6: 93CxxC; SOIC-8_3.9x4.9mm_P1.27mm
U21: NUP2202; SOT-363_SC-70-6
U24: FT2232HL; LQFP-64_10x10mm_P0.5mm
Y2: 12MHZ; Crystal_SMD_0603-2Pin_6.0x3.5mm_HandSoldering

Connections:
+1V8: C27.1, C28.1, C32.1, U24.12 (VCORE), U24.37 (VCORE), U24.49 (VREGOUT), U24.64 (VCORE)
+3.3V: C7.1, C34.1, C49.1, C50.1, C51.1, D2.2 (A), D3.2 (A), FB1.2, FB2.2, R7.2, R26.2, R33.2, R43.1, U6.6 (ORG), U6.8 (VCC), U24.20 (VCCIO), U24.31 (VCCIO), U24.42 (VCCIO), U24.50 (VREGIN), U24.56 (VCCIO)
+5V JTAG-UART: C20.1, C22.1, J6.VBUS1 (VBUS), J6.VBUS2 (VBUS), U21.5
GND: C7.2, C20.2, C22.2, C25.2, C26.2, C27.2, C28.2, C32.2, C34.2, C49.2, C50.2, C51.2, J6.GND, J6.GND2 (GND), J6.SHLD1 (SHLD), J6.SHLD2 (SHLD), J6.SHLD3 (SHLD), J6.SHLD4 (SHLD), J6.SHLD5 (SHLD), J6.SHLD6 (SHLD), J6.SHLD7 (SHLD), J6.SHLD8 (SHLD), R42.1, U6.5 (GND), U21.2, U24.1 (GND), U24.5 (GND), U24.10 (AGND), U24.11 (GND), U24.13 (TEST), U24.15 (GND), U24.25 (GND), U24.35 (GND), U24.47 (GND), U24.51 (GND)
unnamed: C25.1, U24.2 (OSCI), Y2.1
unnamed: C26.1, U24.3 (OSCO), Y2.2
unnamed: D2.1 (K), R44.1
unnamed: D3.1 (K), R45.1
unnamed: FB1.1, U24.4 (VPHY)
unnamed: FB2.1, U24.9 (VPLL)
unnamed: J6.A6 (D+), J6.B6 (D+), R34.1, U21.6
unnamed: J6.A7 (D-), J6.B7 (D-), R38.1, U21.1
unnamed: R7.1, U6.1 (CS), U24.63 (EECS)
unnamed: R26.1, U6.2 (SCLK), U24.62 (EECLK)
unnamed: R33.1, R35.1, U6.4 (DO)
unnamed: R34.2, U24.8 (DP)
unnamed: R35.2, U6.3 (DI), U24.61 (EEDATA)
unnamed: R38.2, U24.7 (DM)
unnamed: R42.2, U24.6 (REF)
unnamed: R43.2, U24.14 (~RESET)
unnamed: R44.2, U24.54 (BCBUS3)
unnamed: R45.2, U24.55 (BCBUS4)
Pogo.TCK: J7.1, U24.16 (ADBUS0)
Pogo.TDI: J7.3, U24.17 (ADBUS1)
Pogo.TDO: J7.4, U24.18 (ADBUS2)
Pogo.TMS: J7.2, U24.19 (ADBUS3)
UART.RX: U24.38 (BDBUS0)
UART.TX: U24.39 (BDBUS1)
