supermomo31/PCE_colorlight_carrier/PCE_Colorlight_Carrier/usb_host.kicad_sch

## KiCad design PCE_Colorlight_Carrier/usb_host.kicad_sch (2026-05-21, an earlier design)

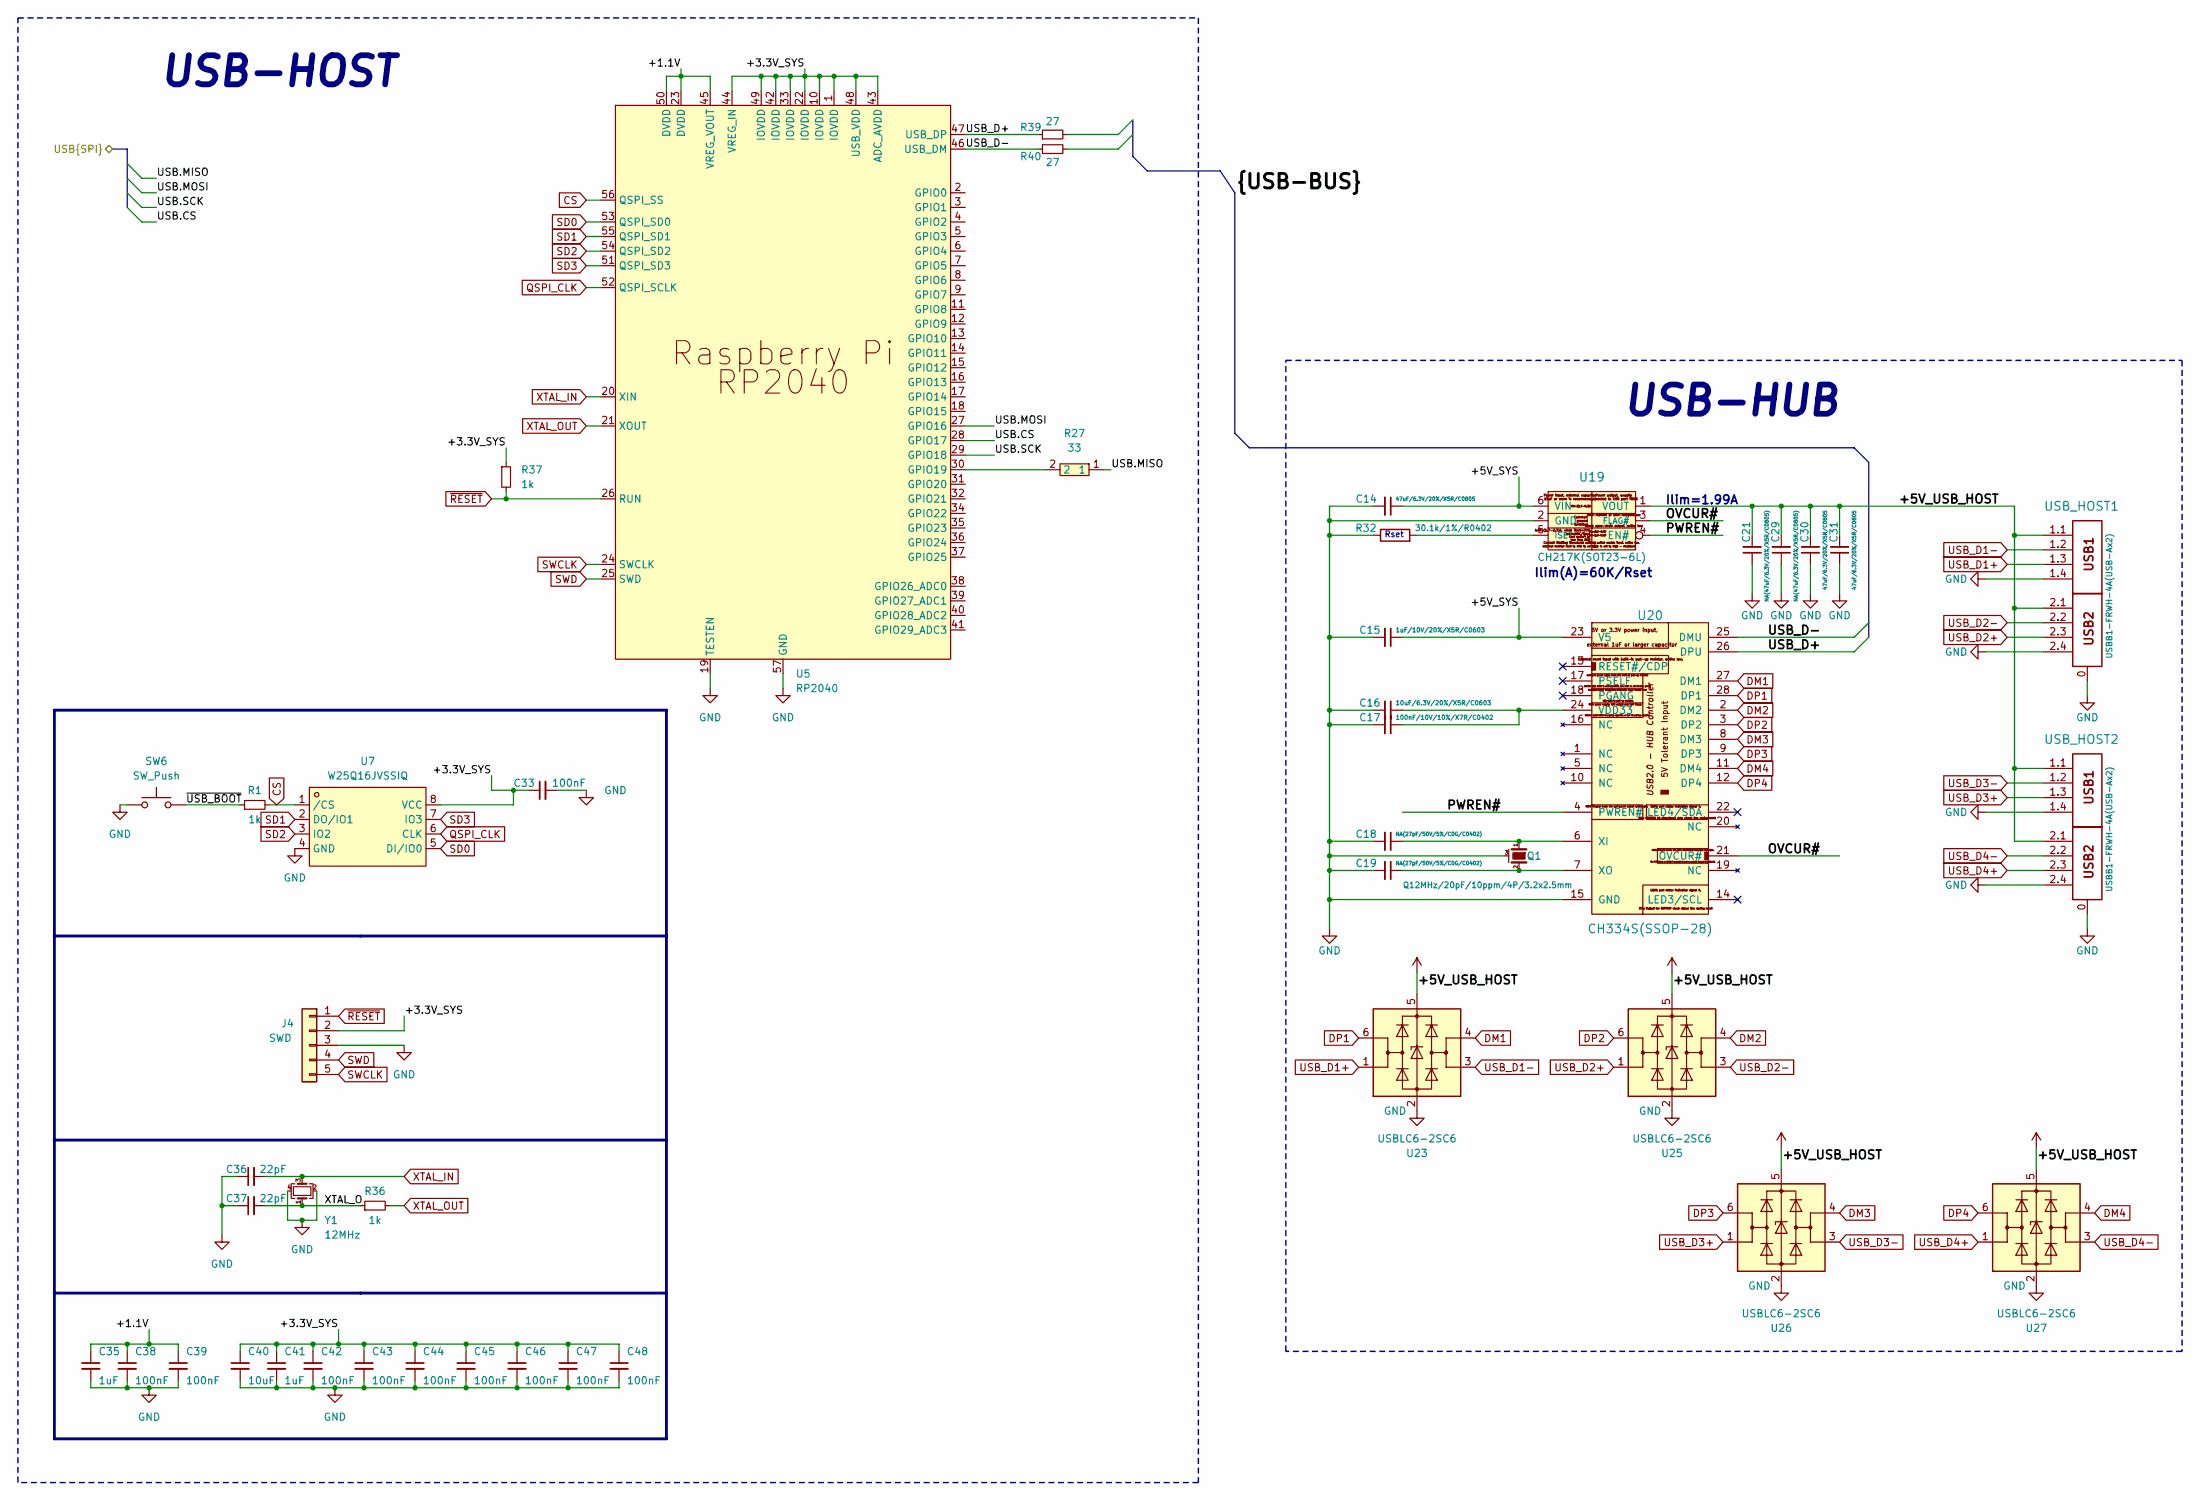
[picture p9: schematic usb_host.kicad_sch]

Parts:
C14, C30, C31: 47uF/6.3V/20%/X5R/C0805; C_0805_5MIL_DWS
C15: 1uF/10V/20%/X5R/C0603; C_0603_5MIL_DWS
C16: 10uF/6.3V/20%/X5R/C0603; C_0603_5MIL_DWS
C17: 100nF/10V/10%/X7R/C0402; C_0402_5MIL_DWS
C18, C19: NA(27pF/50V/5%/C0G/C0402); C_0402_5MIL_DWS
C21, C29: NA(47uF/6.3V/20%/X5R/C0805); C_0805_5MIL_DWS
C33, C38, C39, C42, C43, C44, C45, C46, C47, C48: 100nF; C_0402_1005Metric; LCSC C1525
C35, C41: 1uF; C_0402_1005Metric; LCSC C52923
C36, C37: 22pF; C_0402_1005Metric; LCSC C1555
C40: 10uF; C_0402_1005Metric; LCSC C15525
J4: SWD; PinSocket_1x05_P2.54mm_Vertical
Q1: Q12MHz/20pF/10ppm/4P/3.2x2.5mm; TSX-3.2x2.5mm_GND(3)
R1, R36, R37: 1k; R_0402_1005Metric; LCSC C11702
R27: 33; R0603; MPN 0603WAF5101T5E; LCSC Part C23186
R32: 30.1k/1%/R0402; R_0402_5MIL_DWS
R39, R40: 27; R_0603_1608Metric; LCSC C25190
SW6: SW_Push; PinSocket_1x02_P2.54mm_Vertical
U5: RP2040; MPN RP2040; LCSC Part C2040
U7: W25Q16JVSSIQ; MPN W25Q16JVSSIQ; LCSC Part C82317
U19: CH217K(SOT23-6L); SOT23-6
U20: CH334S(SSOP-28); SSOP28
U23, U25, U26, U27: USBLC6-2SC6; SOT-23-6; LCSC C2827654
USB_HOST1, USB_HOST2: USBB1-FRWH-4A(USB-Ax2); USB_TWO_LEVEL
Y1: 12MHz; Crystal_SMD_3225-4Pin_3.2x2.5mm; LCSC C9002

Connections:
+1.1V: C35.1, C38.1, C39.1, U5.23 (DVDD), U5.45 (VREG_VOUT), U5.50 (DVDD)
+3.3V_SYS: C33.1, C40.1, C41.1, C42.1, C43.1, C44.1, C45.1, C46.1, C47.1, C48.1, J4.2, R37.1, U5.1 (IOVDD), U5.10 (IOVDD), U5.22 (IOVDD), U5.33 (IOVDD), U5.42 (IOVDD), U5.43 (ADC_AVDD), U5.44 (VREG_IN), U5.48 (USB_VDD), U5.49 (IOVDD), U7.8 (VCC)
+5V: C21.2, C29.2, C30.2, C31.2, U19.1 (VOUT), U23.5 (VBUS), U25.5 (VBUS), U26.5 (VBUS), U27.5 (VBUS), USB_HOST1.1.1, USB_HOST1.2.1, USB_HOST2.1.1, USB_HOST2.2.1
+5V_SYS: C14.1, C15.1, U19.6 (VIN), U20.23 (V5)
CS: R1.2, U5.56 (QSPI_SS), U7.1 (/CS)
DM1: U20.27 (DM1), U23.4 (I/O2)
DM2: U20.2 (DM2), U25.4 (I/O2)
DM3: U20.8 (DM3), U26.4 (I/O2)
DM4: U20.11 (DM4), U27.4 (I/O2)
DP1: U20.28 (DP1), U23.6 (I/O1)
DP2: U20.3 (DP2), U25.6 (I/O1)
DP3: U20.9 (DP3), U26.6 (I/O1)
DP4: U20.12 (DP4), U27.6 (I/O1)
GND: C14.2, C15.2, C16.2, C17.2, C18.2, C19.2, C21.1, C29.1, C30.1, C31.1, C33.2, C35.2, C36.1, C37.1, C38.2, C39.2, C40.2, C41.2, C42.2, C43.2, C44.2, C45.2, C46.2, C47.2, C48.2, J4.3, Q1.3 (case), R32.1, SW6.1, U5.19 (TESTEN), U5.57 (GND), U7.4 (GND), U19.2 (GND), U20.15 (GND), U23.2 (GND), U25.2 (GND), U26.2 (GND), U27.2 (GND), USB_HOST1.0, USB_HOST1.1.4, USB_HOST1.2.4, USB_HOST2.0, USB_HOST2.1.4, USB_HOST2.2.4, Y1.2, Y1.4
unnamed: C16.1, C17.1, U20.24 (VDD33)
unnamed: C18.1, Q1.1, U20.6 (XI)
unnamed: C19.1, Q1.2, U20.7 (XO)
unnamed: R27.2, U5.30 (GPIO19)
unnamed: R32.2, U19.5 (ISET)
OVCUR#: U19.3 (FLAG#), U20.21 (OVCUR#)
PWREN#: U19.4 (EN#), U20.4 (PWREN#)
QSPI_CLK: U5.52 (QSPI_SCLK), U7.6 (CLK)
SD0: U5.53 (QSPI_SD0), U7.5 (DI/IO0)
SD1: U5.55 (QSPI_SD1), U7.2 (DO/IO1)
SD2: U5.54 (QSPI_SD2), U7.3 (IO2)
SD3: U5.51 (QSPI_SD3), U7.7 (IO3)
SWCLK: J4.5, U5.24 (SWCLK)
SWD: J4.4, U5.25 (SWD)
USB.CS: U5.28 (GPIO17)
USB.MISO: R27.1
USB.MOSI: U5.27 (GPIO16)
USB.SCK: U5.29 (GPIO18)
USB_D1+: U23.1 (I/O1), USB_HOST1.1.3
USB_D1-: U23.3 (I/O2), USB_HOST1.1.2
USB_D2+: U25.1 (I/O1), USB_HOST1.2.3
USB_D2-: U25.3 (I/O2), USB_HOST1.2.2
USB_D3+: U26.1 (I/O1), USB_HOST2.1.3
USB_D3-: U26.3 (I/O2), USB_HOST2.1.2
USB_D4+: U27.1 (I/O1), USB_HOST2.2.3
USB_D4-: U27.3 (I/O2), USB_HOST2.2.2
USB_D+: R39.1, U5.47 (USB_DP), U20.26 (DPU)
USB_D-: R40.1, U5.46 (USB_DM), U20.25 (DMU)
XTAL_IN: C36.2, U5.20 (XIN), Y1.3
XTAL_O: C37.2, R36.1, Y1.1
XTAL_OUT: R36.2, U5.21 (XOUT)
~RESET: J4.1, R37.2, U5.26 (RUN)
~USB_BOOT: R1.1, SW6.2

Notes on the sheet:
USB-HOST
USB-HUB
Ilim=1.99A
Rset
Ilim(A)=60K/Rset
